nigeljohnson73/neoclock/_app/NjButton.py

from multiprocessing.pool import ApplyResult
import time
from _app.AppLog import AppLog
import digitalio

'''
Handle a simple button that's debounced.
'''


class NjButton():
    def __init__(self, pin, func_press, func_release=None, label=""):
        self.button = digitalio.DigitalInOut(pin)
        self.button.direction = digitalio.Direction.INPUT
        self.button.pull = digitalio.Pull.UP

        self.debounce_delay = 1/100
        self.func_press = func_press
        self.func_release = func_release
        self.label = label
        self.state = self.button.value
        self.last_state = self.state
        self.last_state_time = time.time()

        # print(f"NjButton::NjButton({self.label}): state: {self.state}")
        AppLog.log(f"NjButton::NjButton({self.label})")

    def loop(self):
        self.state = self.button.value
        if self.state != self.last_state:
            now = time.time()
            if (now - self.last_state_time) >= self.debounce_delay:
                # pull up resistor means buton is pressed when state is low
                if not self.state:
                    self.func_press(self.label)
                elif self.func_release:
                    self.func_release(self.label)
                self.last_state_time = now
        self.last_state = self.state
