nigeljohnson73/neoclock/_app/KillableThread.py

import sys
# import trace
import threading

'''
This class wraps the threading functionality
but allows you to nicely(ish) kill a thread from outside.
'''


class KillableThread(threading.Thread):
    def __init__(self, *args, **keywords):
        threading.Thread.__init__(self, *args, **keywords)
        self.killed = False

    def start(self):
        self.__run_backup = self.run
        self.run = self.__run
        threading.Thread.start(self)

    def __run(self):
        sys.settrace(self.globaltrace)
        self.__run_backup()
        self.run = self.__run_backup

    def globaltrace(self, frame, event, arg):
        if event == 'call':
            return self.localtrace
        else:
            return None

    def localtrace(self, frame, event, arg):
        if self.killed:
            if event == 'line':
                raise SystemExit()
        return self.localtrace

    def kill(self):
        self.killed = True
        # self.join() # Call this yourself from outside
